PocketMidi/KB1/references/firmware/middle - c.png

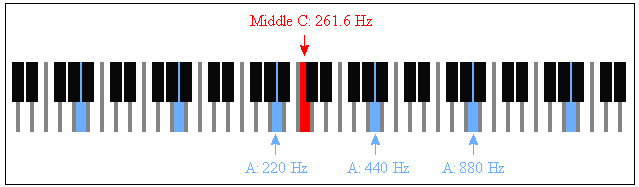
references/firmware/middle - c.png
