PocketMidi/KB1/references/hardware/Seeed_xiao_ESP32-S3/2.jpg

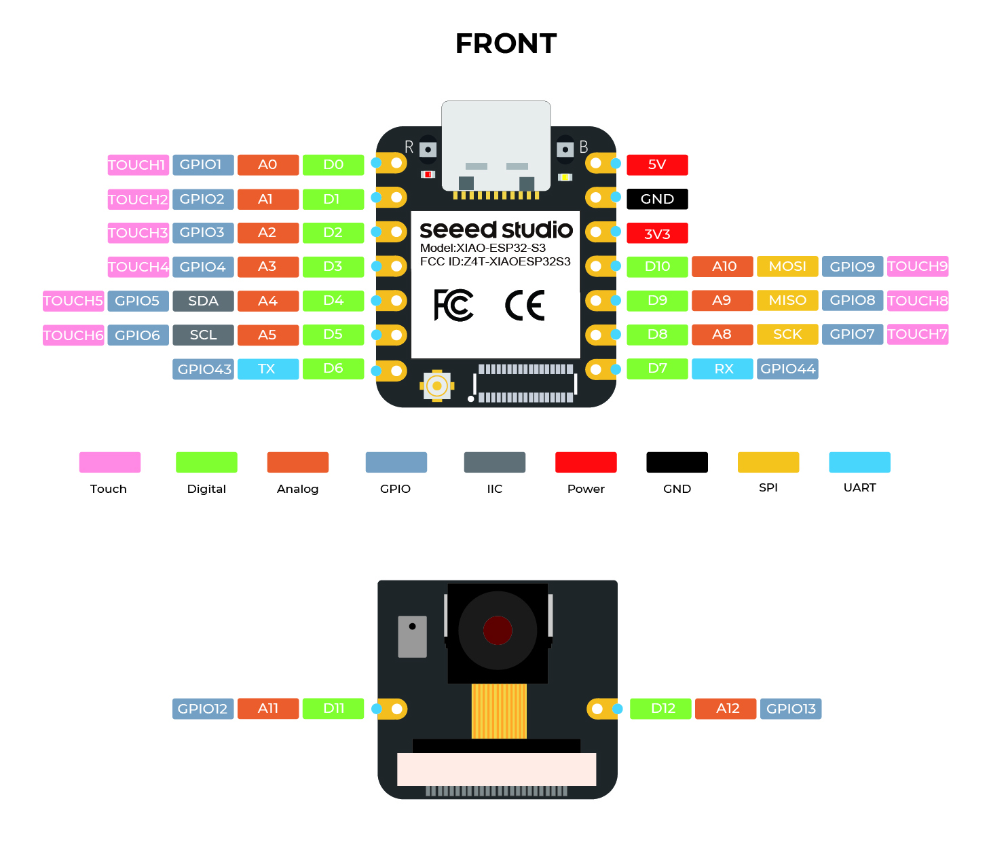
references/hardware/Seeed_xiao_ESP32-S3/2.jpg
