PocketMidi/KB1/references/hardware/Seeed_xiao_ESP32-S3/3.png

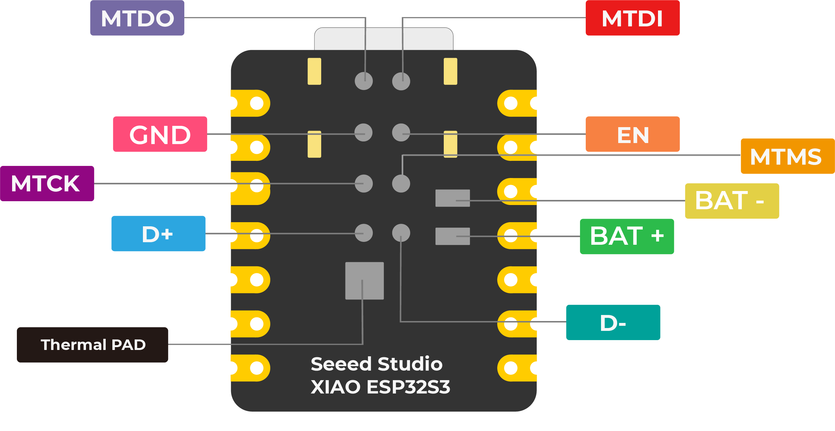
references/hardware/Seeed_xiao_ESP32-S3/3.png
