PocketMidi/KB1/hardware/mechanicals/STLs/Wedge R1.stl

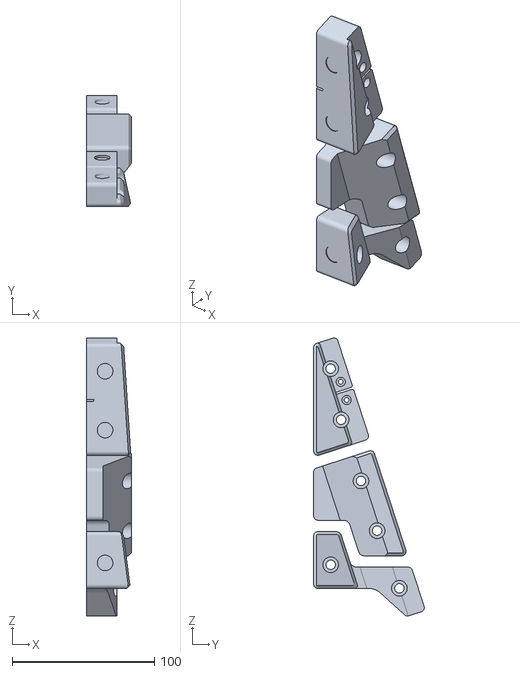
[picture p28: CAD file, 2024-06-25]
hardware/mechanicals/STLs/Wedge R1.stl
31.5 x 77.9 x 195.7
