PocketMidi/KB1/hardware/mechanicals/STLs/Wedge Keeper.stl

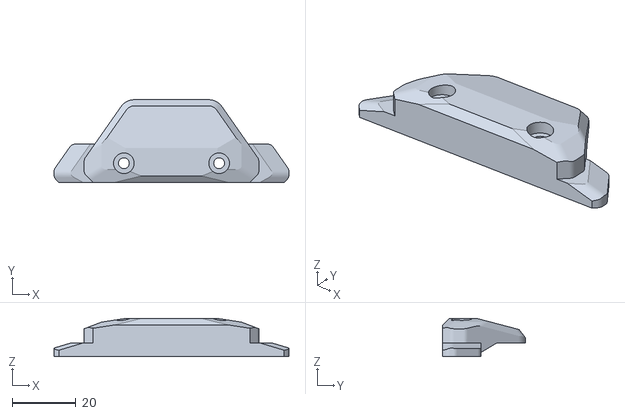
[picture p29: CAD file, 2024-06-25]
hardware/mechanicals/STLs/Wedge Keeper.stl
74.0 x 26.0 x 12.0
