PocketMidi/KB1/hardware/mechanicals/STLs/Wedge_center.stl

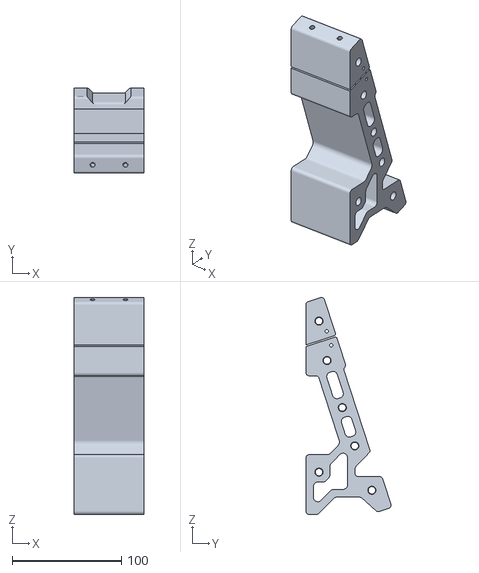
[picture p30: CAD file, 2024-06-25]
hardware/mechanicals/STLs/Wedge_center.stl
64.0 x 77.9 x 198.3
