PocketMidi/KB1/assets/installation/complete.png

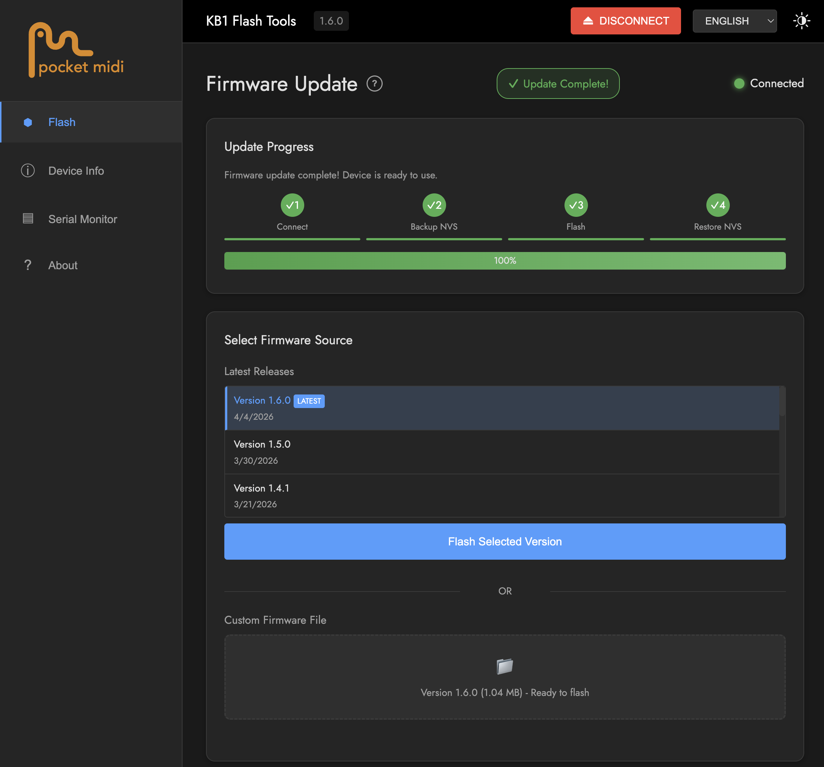
assets/installation/complete.png
