PocketMidi/KB1/firmware/src/objects/Constants.h

#ifndef CONSTANTS_H
#define CONSTANTS_H

// Firmware version
#define FIRMWARE_VERSION "2.3.3"
#define FIRMWARE_VERSION_MAJOR 2
#define FIRMWARE_VERSION_MINOR 3
#define FIRMWARE_VERSION_PATCH 3

// Uncomment following line to enable Serial Printing
#define SERIAL_PRINT_ENABLED 1

// Pin definitions for U1
#define SWD1_LEFT_PIN 5   // SWD1 Left button pin
#define SWD1_CENTER_PIN 6 // SWD1 Center button pin

// Pin definitions for U2
#define SWD1_RIGHT_PIN 0  // SWD1 Right button pin
#define SWD2_LEFT_PIN 1   // SWD2 Left button pin
#define SWD2_CENTER_PIN 2 // SWD2 Center button pin
#define SWD2_RIGHT_PIN 3  // SWD2 Right button pin

#define SERVICE_UUID             "f22b99e8-81ab-4e46-abff-79a74a1f2ff3"
#define LEVER1_SETTINGS_UUID     "6bae0d4d-a0a4-4bc6-9802-a5d27fb15680"
#define LEVERPUSH1_SETTINGS_UUID "1de84ff3-36c0-4cf6-912b-208600cf94f4"
#define LEVER2_SETTINGS_UUID     "13ffbea4-793f-40f5-82da-ac9eca5f0e09"
#define LEVERPUSH2_SETTINGS_UUID "52629808-3d14-4ae8-a826-40bcec6467d5"
#define TOUCH_SETTINGS_UUID      "5612b54d-8bfe-4217-a079-c9c95ab32c41"
#define SCALE_SETTINGS_UUID      "297bd635-c3e8-4fb4-b5e0-93586da8f14c"
#define CHORD_SETTINGS_UUID      "4a8c9f2e-1b7d-4e3f-a5c6-d7e8f9a0b1c2"
#define STRUM_INTERVALS_UUID     "7f3e2d1c-0a9b-8c7d-6e5f-4a3b2c1d0e9f"
#define SYSTEM_SETTINGS_UUID     "8f7e6d5c-4b3a-2c1d-0e9f-8a7b6c5d4e3f"
#define MIDI_UUID                "eb58b31b-d963-4c7d-9a11-e8aabec2fe32"
#define KEEPALIVE_UUID           "a8f3d5e2-9c4b-11ef-8e7a-325096b39f47"

// Firmware Version UUID (read-only)
#define FIRMWARE_VERSION_UUID    "f3b2c1a0-5e4d-3c2b-1a0f-9e8d7c6b5a4f"

// Preset Management UUIDs
#define PRESET_SAVE_UUID         "d3a7b321-0001-4000-8000-000000000009"
#define PRESET_LOAD_UUID         "d3a7b321-0001-4000-8000-00000000000a"
#define PRESET_LIST_UUID         "d3a7b321-0001-4000-8000-00000000000b"
#define PRESET_DELETE_UUID       "d3a7b321-0001-4000-8000-00000000000c"

// Keep-alive timing constants (in milliseconds)
#define KEEPALIVE_GRACE_PERIOD_MS 600000  // 10 minutes

// Battery Status UUID (read-only)
#define BATTERY_STATUS_UUID      "a1b2c3d4-5e6f-7a8b-9c0d-1e2f3a4b5c6d"
// Battery Control UUID (write - for commands like reset/recalibrate)
#define BATTERY_CONTROL_UUID     "a1b2c3d4-5e6f-7a8b-9c0d-1e2f3a4b5c6e"

// Battery monitoring constants
#define BATTERY_CAPACITY_MAH 420          // Battery capacity in mAh
#define BATTERY_CHARGE_CURRENT_MA 100     // Charging current in mA
#define BATTERY_FULL_CHARGE_MS 18000000   // 5 hours (18000000ms)

// Power consumption by mode (measured values)
#define BATTERY_ACTIVE_DRAIN_MA 35        // Active mode, BLE disconnected (35mA - lowest, no radio)
#define BATTERY_LIGHT_SLEEP_DRAIN_MA 2    // Light sleep current draw
#define BATTERY_DEEP_SLEEP_DRAIN_MA 0.014 // Deep sleep current draw (14µA)

// BLE adaptive power mode drain rates (v1.7.0)
#define BATTERY_BLE_LIVE_DRAIN_MA 95      // BLE LIVE_PERFORMANCE mode (max responsiveness)
#define BATTERY_BLE_CONFIG_DRAIN_MA 60    // BLE CONFIGURATION mode (good responsiveness)
#define BATTERY_BLE_IDLE_DRAIN_MA 50      // BLE IDLE_CONNECTED mode (radio on but idle)

#endif
