PocketMidi/KB1/firmware/src/led/LEDController.cpp

#include "LEDController.h"
#include <freertos/semphr.h>

// Helper function for linear interpolation
float lerp(float a, float b, float f) {
    return a + f * (b - a);
}

LEDController::LEDController() {
    // Initialize LED states
    pinkLed.pin = -1;
    pinkLed.mcp = nullptr;
    pinkLed.mode = LedMode::STATIC;
    pinkLed.currentBrightness = 0;
    pinkLed.targetBrightness = 0;
    pinkLed.startBrightness = 0;
    pinkLed.startTime = 0;
    pinkLed.duration = 0;
    pinkLed.pulseDuration = 0;

    blueLed.pin = -1;
    blueLed.mcp = nullptr;
    blueLed.mode = LedMode::STATIC;
    blueLed.currentBrightness = 0;
    blueLed.targetBrightness = 0;
    blueLed.startBrightness = 0;
    blueLed.startTime = 0;
    blueLed.duration = 0;
    blueLed.pulseDuration = 0;

    octaveUpLed.pin = -1;
    octaveUpLed.mcp = nullptr;
    octaveUpLed.mode = LedMode::STATIC;
    octaveUpLed.currentBrightness = 0;
    octaveUpLed.targetBrightness = 0;
    octaveUpLed.startBrightness = 0;
    octaveUpLed.startTime = 0;
    octaveUpLed.duration = 0;
    octaveUpLed.pulseDuration = 0;

    octaveDownLed.pin = -1;
    octaveDownLed.mcp = nullptr;
    octaveDownLed.mode = LedMode::STATIC;
    octaveDownLed.currentBrightness = 0;
    octaveDownLed.targetBrightness = 0;
    octaveDownLed.startBrightness = 0;
    octaveDownLed.startTime = 0;
    octaveDownLed.duration = 0;
    octaveDownLed.pulseDuration = 0;

    // Create a recursive mutex to protect LEDController when accessed from multiple tasks
    _mutex = xSemaphoreCreateRecursiveMutex();
}

LEDController::~LEDController() {
    if (_mutex) {
        vSemaphoreDelete(_mutex);
        _mutex = NULL;
    }
}


void LEDController::begin(LedColor color, int pin, Adafruit_MCP23X17* mcp) {
    if (_mutex) xSemaphoreTakeRecursive(_mutex, portMAX_DELAY);
    LedState* led = nullptr;
    switch (color) {
        case LedColor::PINK:
            led = &pinkLed;
            break;
        case LedColor::BLUE:
            led = &blueLed;
            break;
        case LedColor::OCTAVE_UP:
            led = &octaveUpLed;
            break;
        case LedColor::OCTAVE_DOWN:
            led = &octaveDownLed;
            break;
    }

    if (led) {
        led->pin = pin;
        led->mcp = mcp;
        if (mcp) {
            mcp->pinMode(pin, OUTPUT);
            mcp->digitalWrite(pin, HIGH);
        } else {
            pinMode(led->pin, OUTPUT);
            analogWrite(led->pin, led->currentBrightness);
        }
    }
    if (_mutex) xSemaphoreGiveRecursive(_mutex);
}

void LEDController::set(LedColor color, int targetBrightness, unsigned long duration) {
    if (_mutex) xSemaphoreTakeRecursive(_mutex, portMAX_DELAY);
    LedState* led = nullptr;
    switch (color) {
        case LedColor::PINK:
            led = &pinkLed;
            break;
        case LedColor::BLUE:
            led = &blueLed;
            break;
        case LedColor::OCTAVE_UP:
            led = &octaveUpLed;
            break;
        case LedColor::OCTAVE_DOWN:
            led = &octaveDownLed;
            break;
    }

    if (led) {
        led->mode = LedMode::STATIC;
        led->targetBrightness = constrain(targetBrightness, 0, 255);
        led->startBrightness = led->currentBrightness;
        led->startTime = millis();
        led->duration = duration;
        if (duration == 0) {
            led->currentBrightness = led->targetBrightness;
            if (led->mcp) {
                led->mcp->digitalWrite(led->pin, led->currentBrightness > 0 ? LOW : HIGH);
            } else {
                analogWrite(led->pin, led->currentBrightness);
            }
        }
    }
    if (_mutex) xSemaphoreGiveRecursive(_mutex);
}

void LEDController::pulse(LedColor color, unsigned long pulseSpeed, unsigned long totalPulsationDuration) {
    if (_mutex) xSemaphoreTakeRecursive(_mutex, portMAX_DELAY);
    LedState* led = nullptr;
    switch (color) {
        case LedColor::PINK:
            led = &pinkLed;
            break;
        case LedColor::BLUE:
            led = &blueLed;
            break;
        case LedColor::OCTAVE_UP:
            led = &octaveUpLed;
            break;
        case LedColor::OCTAVE_DOWN:
            led = &octaveDownLed;
            break;
    }

    if (led) {
        led->mode = LedMode::PULSE;
        led->pulseDuration = (pulseSpeed == 0) ? 1 : pulseSpeed;
        led->duration = totalPulsationDuration;
        led->startTime = millis();
    }
    if (_mutex) xSemaphoreGiveRecursive(_mutex);
}

void LEDController::update() {
    if (_mutex) xSemaphoreTakeRecursive(_mutex, portMAX_DELAY);
    updateLed(pinkLed);
    updateLed(blueLed);
    updateLed(octaveUpLed);
    updateLed(octaveDownLed);
    if (_mutex) xSemaphoreGiveRecursive(_mutex);
}

void LEDController::updateLed(LedState& led) {
    if (led.pin == -1) {
        // LED not initialized
        return;
    }

    unsigned long currentTime = millis();
    unsigned long elapsedTime = currentTime - led.startTime;

    if (led.mcp) { // MCP-controlled LED (digital, active-low)
        if (led.mode == LedMode::STATIC) {
            if (elapsedTime >= led.duration) {
                led.currentBrightness = led.targetBrightness;
                led.mcp->digitalWrite(led.pin, led.currentBrightness > 0 ? LOW : HIGH);
            } else {
                // No interpolation for MCP, just wait until duration ends
            }
        } else if (led.mode == LedMode::PULSE) {
            if (led.duration != 0 && elapsedTime >= led.duration) {
                // Stop pulsing after total duration
                led.mode = LedMode::STATIC;
                led.currentBrightness = 0;
                if (led.mcp) {
                    led.mcp->digitalWrite(led.pin, HIGH); // Turn off for active-low
                } else {
                    analogWrite(led.pin, 0);
                }
                return; // Exit update for this LED
            }
            float progress = (float)(elapsedTime % led.pulseDuration) / (float)led.pulseDuration;
            int state = progress < 0.5f ? LOW : HIGH; // 50% duty cycle
            led.mcp->digitalWrite(led.pin, state);
            led.currentBrightness = (state == LOW) ? 255 : 0;
        }
    } else { // GPIO-controlled LED (analog)
        if (led.mode == LedMode::STATIC) {
            if (elapsedTime < led.duration) {
                float progress = (float)elapsedTime / (float)led.duration;
                led.currentBrightness = (int)lerp(led.startBrightness, led.targetBrightness, progress);
                analogWrite(led.pin, led.currentBrightness);
            } else {
                led.currentBrightness = led.targetBrightness;
                analogWrite(led.pin, led.currentBrightness);
            }
        } else if (led.mode == LedMode::PULSE) {
            if (led.duration != 0 && elapsedTime >= led.duration) {
                // Stop pulsing after total duration
                led.mode = LedMode::STATIC;
                led.currentBrightness = 0;
                analogWrite(led.pin, 0);
                return; // Exit update for this LED
            }
            float progress = (float)(elapsedTime % led.pulseDuration) / (float)led.pulseDuration;
            float brightness;
            if (progress < 0.5f) {
                // Fade in
                brightness = 2.0f * progress;
            } else {
                // Fade out
                brightness = 2.0f * (1.0f - progress);
            }
            led.currentBrightness = (int)(brightness * 255.0f);
            analogWrite(led.pin, led.currentBrightness);
        }
    }
}
